johneast2/keychainbackup/manageApp/assets/keychainpic.png

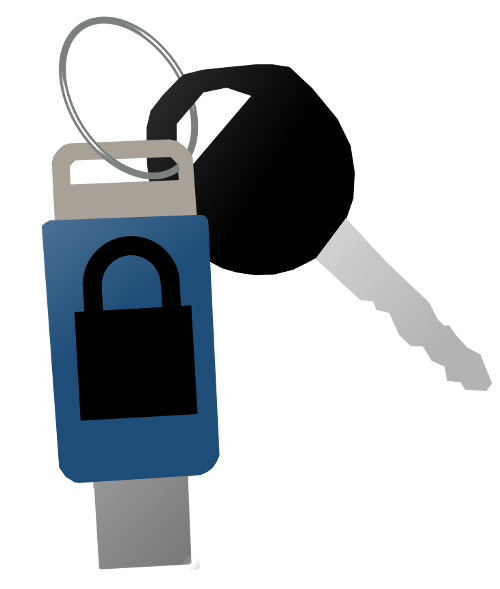
manageApp/assets/keychainpic.png
