johneast2/keychainbackup/pictures/after_login.png

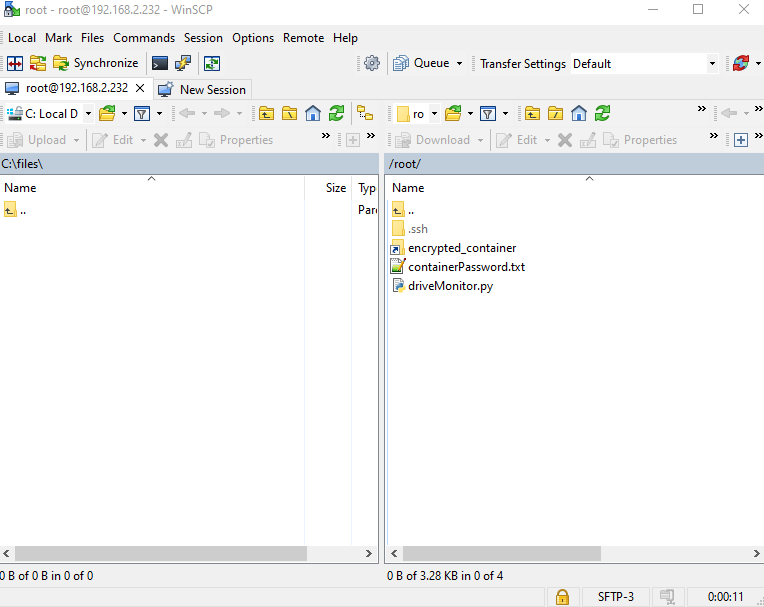
pictures/after_login.png
