johneast2/keychainbackup/pictures/no_encryption_warning_last.png

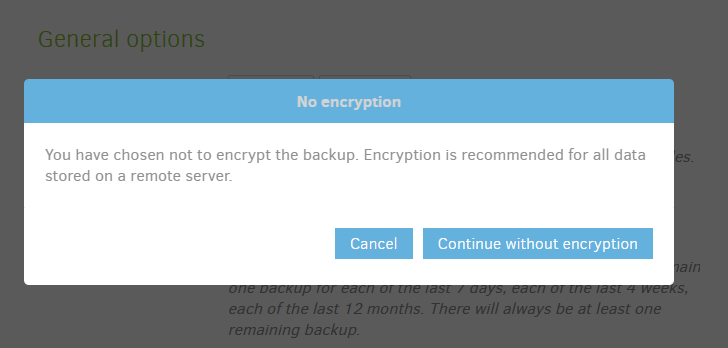
pictures/no_encryption_warning_last.png
