johneast2/keychainbackup/pictures/pulloutbluearrow.png

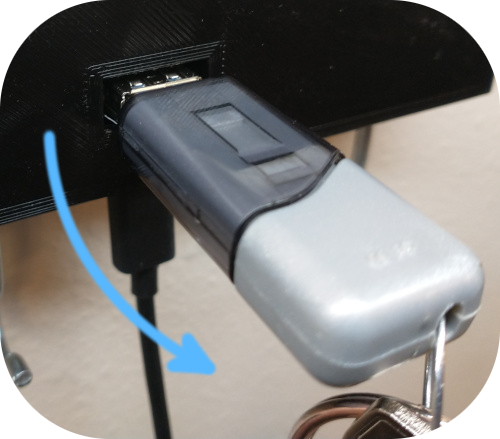
pictures/pulloutbluearrow.png
